svirant/DonutHole/images/7.png

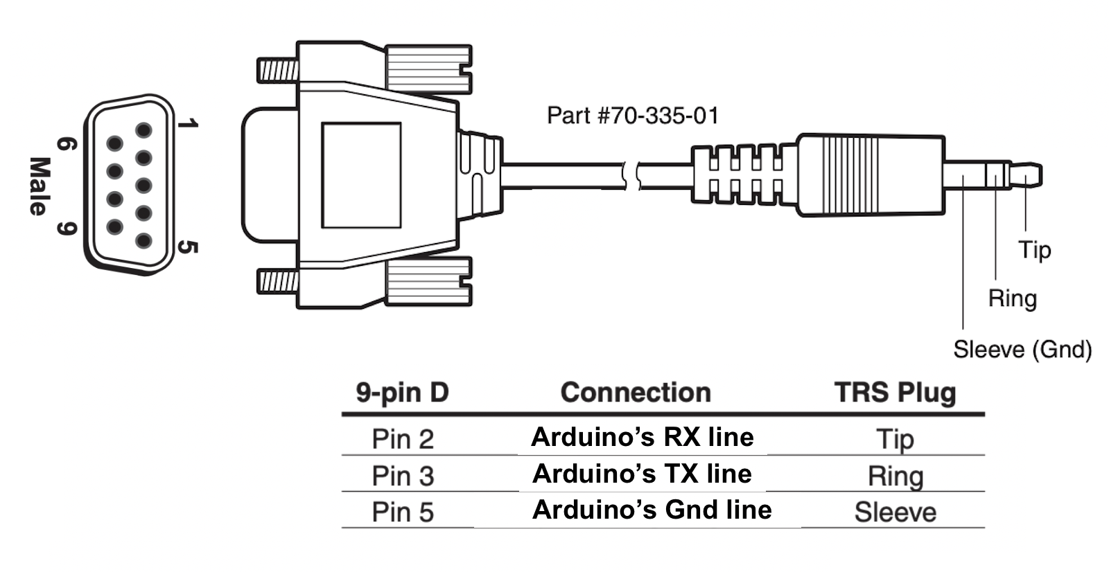
images/7.png
